svenschwermer/open-esp-webradio/include/mi0283qt.h

#ifndef _MI0283QT_H_
#define _MI0283QT_H_

#include <stdbool.h>
#include <stddef.h>
#include <stdint.h>

#define LCD_WIDTH 240
#define LCD_HEIGHT 320

// values 0..63
static inline uint16_t RGB(uint16_t r, uint16_t g, uint16_t b) {
  // g2 g1 g0 b5 b4 b3 b2 b1   r5 r4 r3 r2 r1 g5 g4 g3

  return ((g & 0x07) << 15) | ((b & 0x3e) << 7) | ((r & 0x3e) << 2) |
         ((g & 0x38) >> 3);
}

int lcd_init(void);
void lcd_set_area(uint16_t x0, uint16_t y0, uint16_t x1, uint16_t y1);
void lcd_write_pixels(size_t count, const uint16_t *pixels);
void lcd_rect(uint16_t color, uint16_t x0, uint16_t y0, uint16_t x1,
              uint16_t y1);
void lcd_fill(uint16_t color);
void lcd_xy_exchange(bool exchange);
int lcd_string(int x, int y, const char *str);
int lcd_stringn(int x, int y, const char *str, size_t n);
void lcd_scroll_on(uint16_t top_fixed, uint16_t bottom_fixed);
void lcd_scroll(uint16_t lines);

#endif
