svenschwermer/open-esp-webradio/include/crc_config_user.h

#ifndef INCLUDE_CRC_CONFIG_USER_H_
#define INCLUDE_CRC_CONFIG_USER_H_

#include <stdint.h>

#define CRC_DEBUG 0
#define CRC_1BYTE_SUPPORT 1
#define CRC_4BYTE_SUPPORT 0
#define CRC_8BYTE_SUPPORT 0

typedef uint8_t     crc_8;
typedef uint16_t    crc_16;
typedef uint32_t    crc_32;
typedef uint64_t    crc_64;

#endif /* INCLUDE_CRC_CONFIG_USER_H_ */
